CNMAT/CNMAT-PC2410/Frequency Response/Screen Shot 2022-06-17 at 10.40.44 AM.png

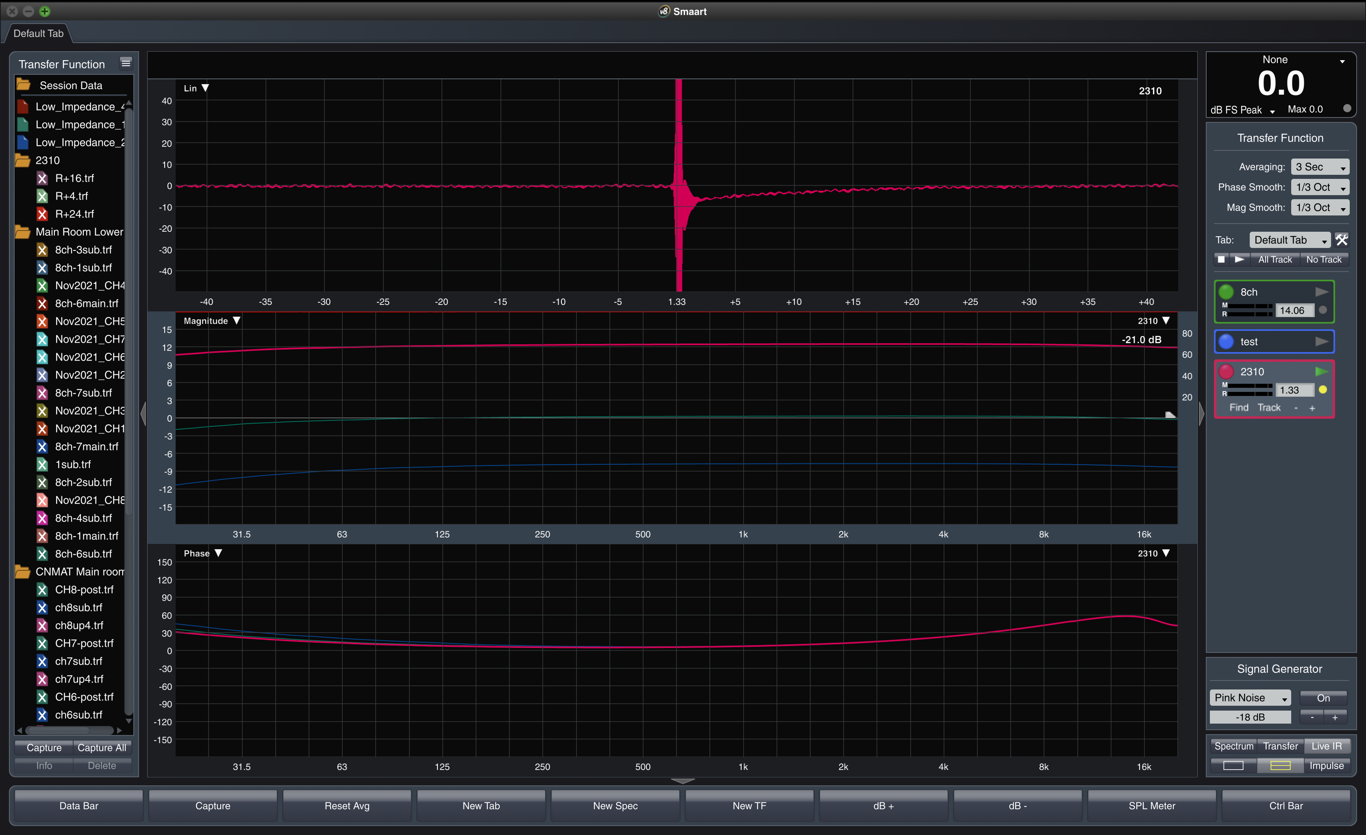
Frequency Response/Screen Shot 2022-06-17 at 10.40.44 AM.png
